joostwijn/Hard_Versus_Soft_Magnetic_Microrobots/4. Microrobots/Designs/Ribbon_Hard_Magnet.SLDPRT

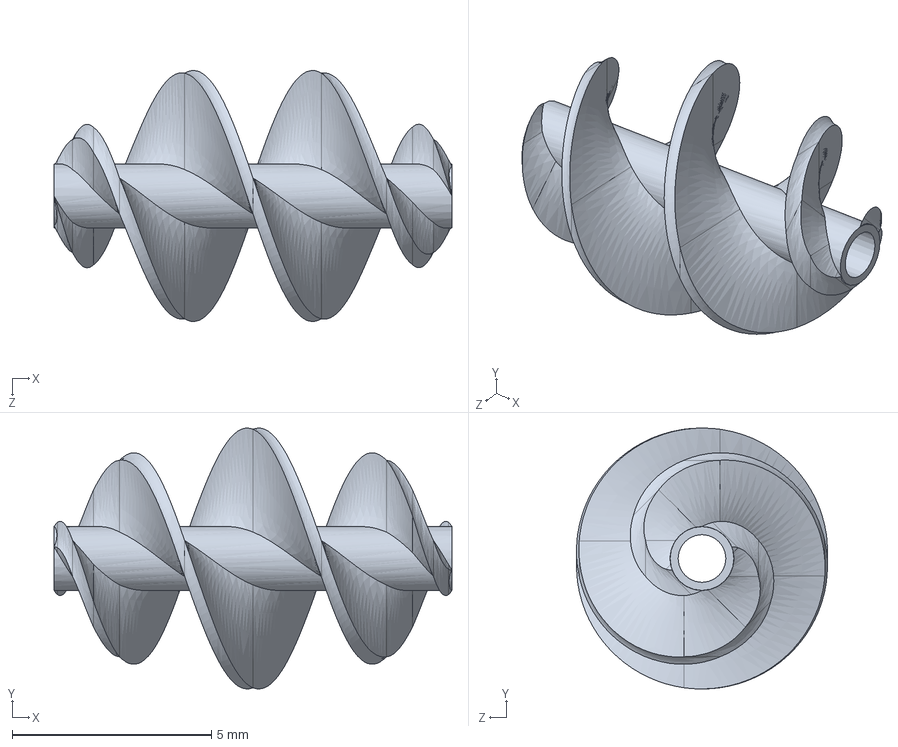
[picture p15: CAD file, 2025-07-08]
4. Microrobots/Designs/Ribbon_Hard_Magnet.SLDPRT
10.00 x 6.55 x 6.31 mm
