joostwijn/Hard_Versus_Soft_Magnetic_Microrobots/1. Rotating Magnetic Field Setup/DXF/PMMA_3mm_1x_FrontP.DXF

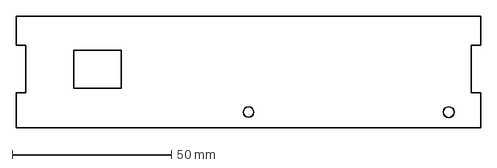
[picture p16: CAD file, 2025-07-07]
1. Rotating Magnetic Field Setup/DXF/PMMA_3mm_1x_FrontP.DXF
146.0 x 35.2 mm
