joostwijn/Hard_Versus_Soft_Magnetic_Microrobots/1. Rotating Magnetic Field Setup/SLDPRT/Plain_Bushing_16x18x20.SLDPRT

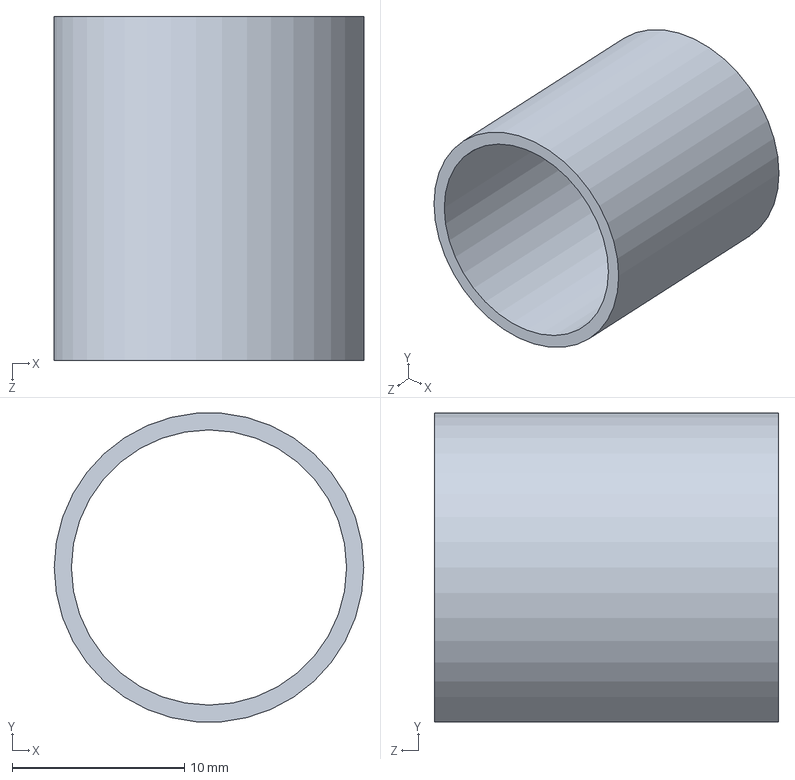
[picture p17: CAD file, 2025-07-07]
1. Rotating Magnetic Field Setup/SLDPRT/Plain_Bushing_16x18x20.SLDPRT
18.0 x 17.9 x 20.0 mm
