joostwijn/Hard_Versus_Soft_Magnetic_Microrobots/4. Microrobots/Designs/Tapered_Helix_Soft_Magnet.SLDPRT

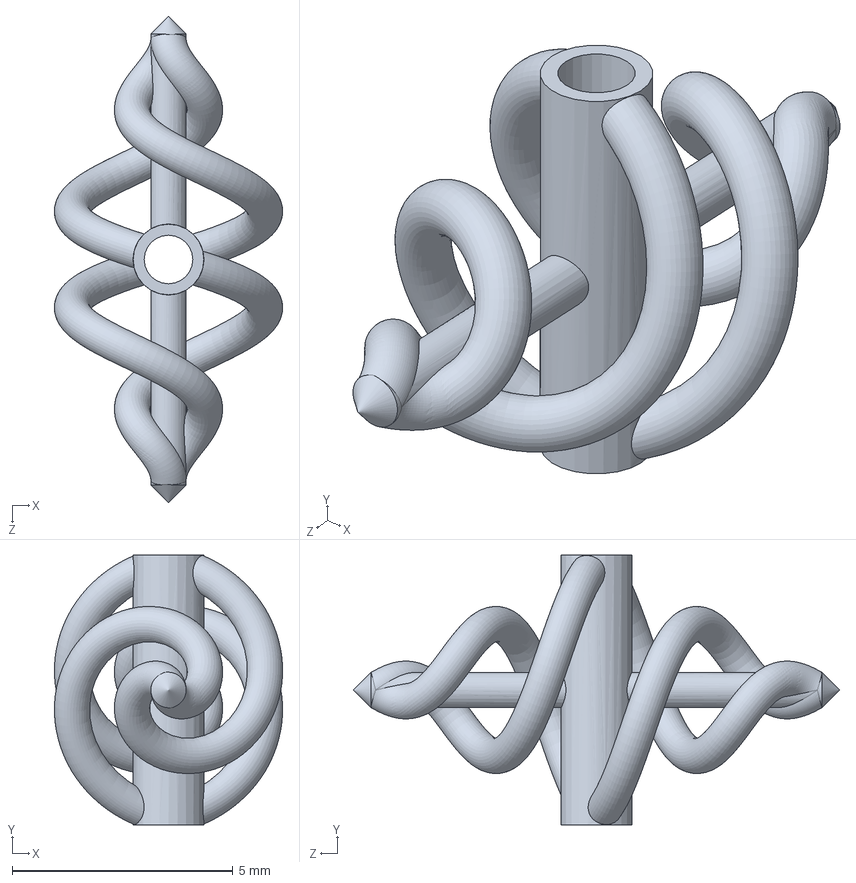
[picture p18: CAD file, 2025-07-08]
4. Microrobots/Designs/Tapered_Helix_Soft_Magnet.SLDPRT
5.16 x 6.10 x 11.0 mm
