joostwijn/Hard_Versus_Soft_Magnetic_Microrobots/1. Rotating Magnetic Field Setup/DXF/PMMA_3mm_1x_RightSP.DXF

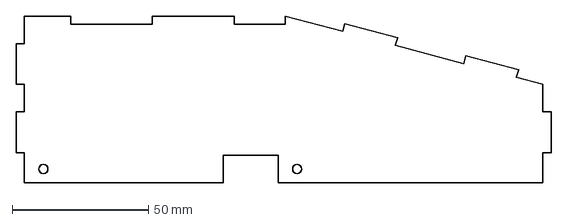
[picture p19: CAD file, 2025-07-07]
1. Rotating Magnetic Field Setup/DXF/PMMA_3mm_1x_RightSP.DXF
196.0 x 61.0 mm
