joostwijn/Hard_Versus_Soft_Magnetic_Microrobots/1. Rotating Magnetic Field Setup/SLDPRT/Slots.SLDPRT

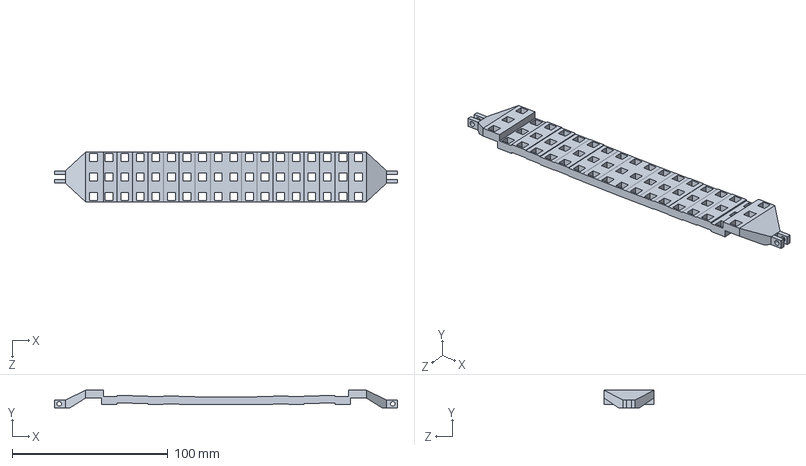
[picture p20: CAD file, 2025-07-07]
1. Rotating Magnetic Field Setup/SLDPRT/Slots.SLDPRT
220.0 x 11.3 x 32.0 mm
