joostwijn/Hard_Versus_Soft_Magnetic_Microrobots/1. Rotating Magnetic Field Setup/SLDPRT/O-Ring_6x1.9.SLDPRT

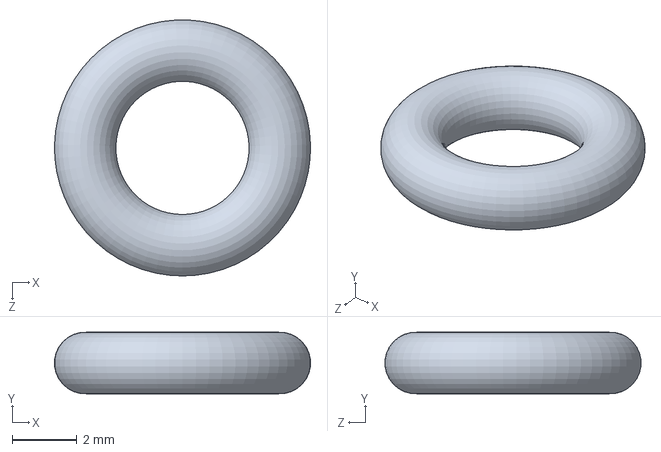
[picture p21: CAD file, 2025-07-07]
1. Rotating Magnetic Field Setup/SLDPRT/O-Ring_6x1.9.SLDPRT
7.89 x 1.90 x 7.88 mm
