joostwijn/Hard_Versus_Soft_Magnetic_Microrobots/1. Rotating Magnetic Field Setup/SLDPRT/Mounting_Bracket_ NEMA17.SLDPRT

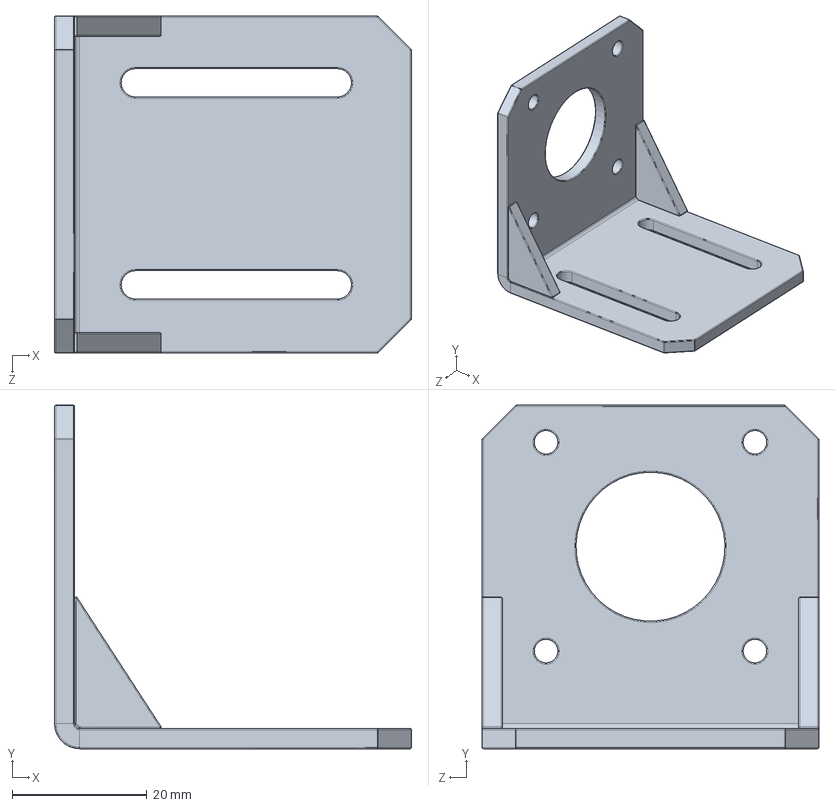
[picture p22: CAD file, 2025-07-07]
1. Rotating Magnetic Field Setup/SLDPRT/Mounting_Bracket_ NEMA17.SLDPRT
53.0 x 51.0 x 50.0 mm
