joostwijn/Hard_Versus_Soft_Magnetic_Microrobots/1. Rotating Magnetic Field Setup/SLDPRT/NX3224T024.SLDPRT

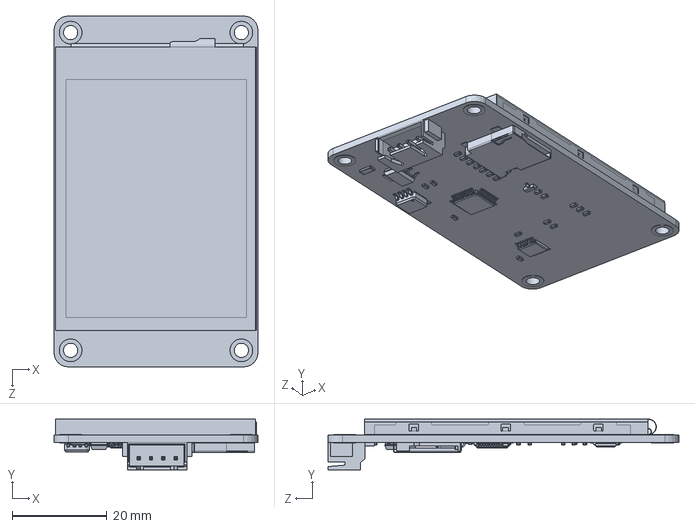
[picture p23: CAD file, 2025-07-07]
1. Rotating Magnetic Field Setup/SLDPRT/NX3224T024.SLDPRT
43.0 x 10.7 x 74.0 mm
