joostwijn/Hard_Versus_Soft_Magnetic_Microrobots/1. Rotating Magnetic Field Setup/SLDPRT/PowerSupply.SLDPRT

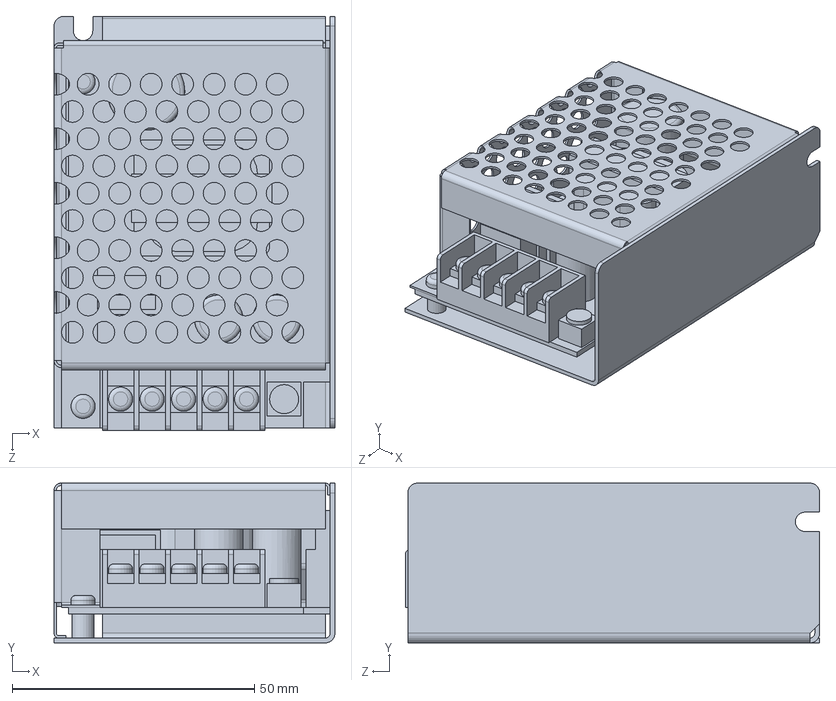
[picture p25: CAD file, 2025-07-07]
1. Rotating Magnetic Field Setup/SLDPRT/PowerSupply.SLDPRT
58.0 x 33.0 x 85.5 mm
