joostwijn/Hard_Versus_Soft_Magnetic_Microrobots/1. Rotating Magnetic Field Setup/SLDPRT/BackPlate.SLDPRT

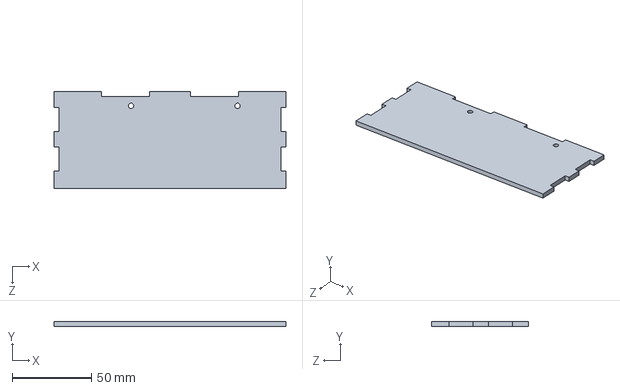
[picture p26: CAD file, 2025-07-07]
1. Rotating Magnetic Field Setup/SLDPRT/BackPlate.SLDPRT
146.0 x 3.00 x 61.0 mm
