joostwijn/Hard_Versus_Soft_Magnetic_Microrobots/1. Rotating Magnetic Field Setup/SLDPRT/Bracket_90deg.SLDPRT

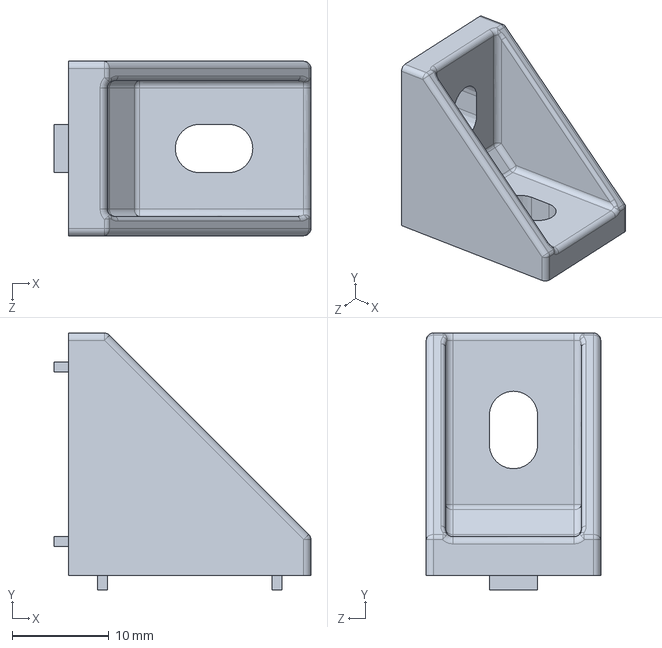
[picture p27: CAD file, 2025-07-07]
1. Rotating Magnetic Field Setup/SLDPRT/Bracket_90deg.SLDPRT
26.5 x 26.5 x 18.0 mm
