joostwijn/Hard_Versus_Soft_Magnetic_Microrobots/1. Rotating Magnetic Field Setup/SLDPRT/Tube_Setter.SLDPRT

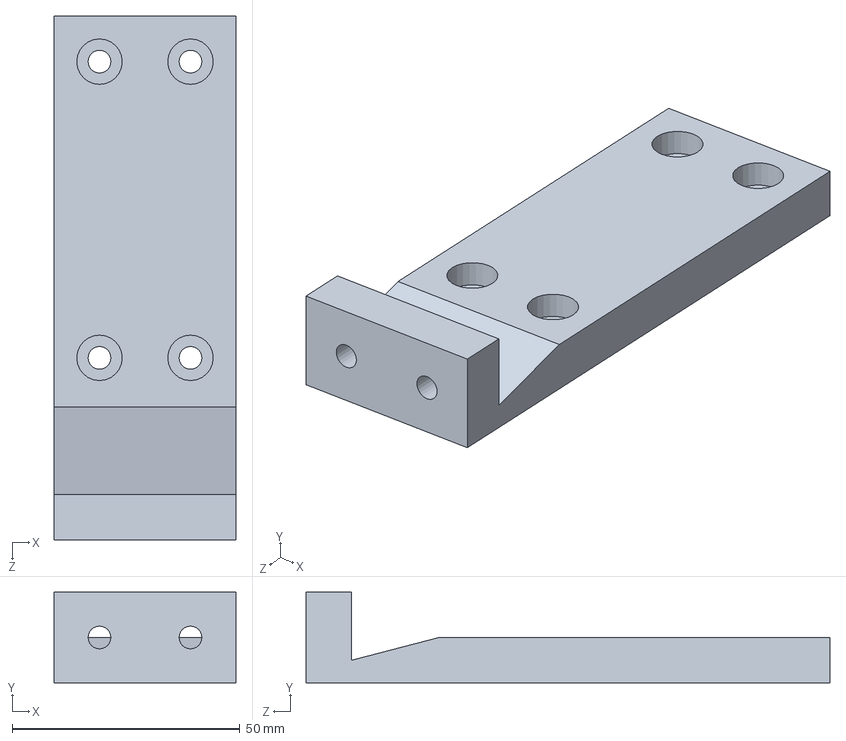
[picture p28: CAD file, 2025-07-07]
1. Rotating Magnetic Field Setup/SLDPRT/Tube_Setter.SLDPRT
40.0 x 20.0 x 115.1 mm
