joostwijn/Hard_Versus_Soft_Magnetic_Microrobots/1. Rotating Magnetic Field Setup/SLDPRT/O-Ring_28x3.1.SLDPRT

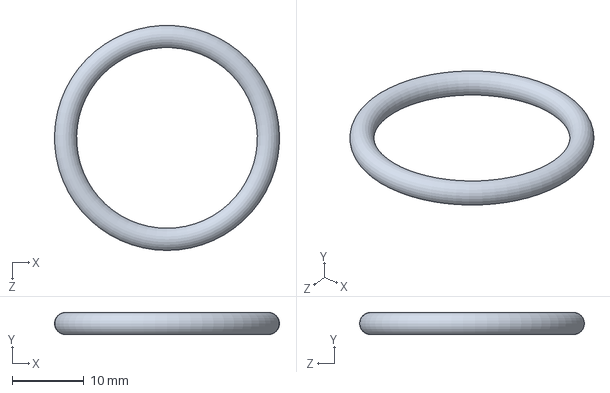
[picture p29: CAD file, 2025-07-07]
1. Rotating Magnetic Field Setup/SLDPRT/O-Ring_28x3.1.SLDPRT
31.4 x 3.10 x 31.4 mm
