joostwijn/Hard_Versus_Soft_Magnetic_Microrobots/1. Rotating Magnetic Field Setup/SLDPRT/FrontPlate.SLDPRT

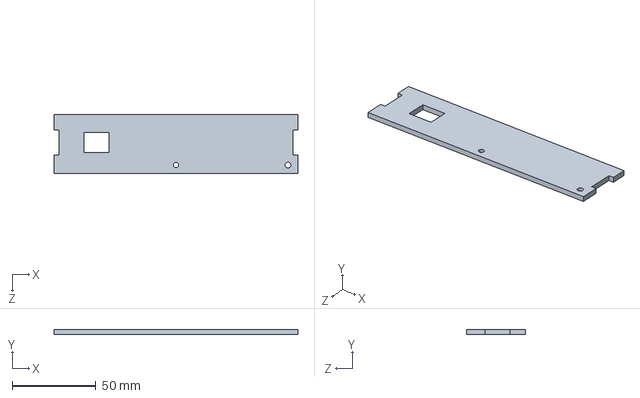
[picture p30: CAD file, 2025-07-07]
1. Rotating Magnetic Field Setup/SLDPRT/FrontPlate.SLDPRT
146.0 x 3.00 x 35.2 mm
