joostwijn/Hard_Versus_Soft_Magnetic_Microrobots/1. Rotating Magnetic Field Setup/SLDPRT/Arduino_UNO_Rev3_Base.SLDPRT

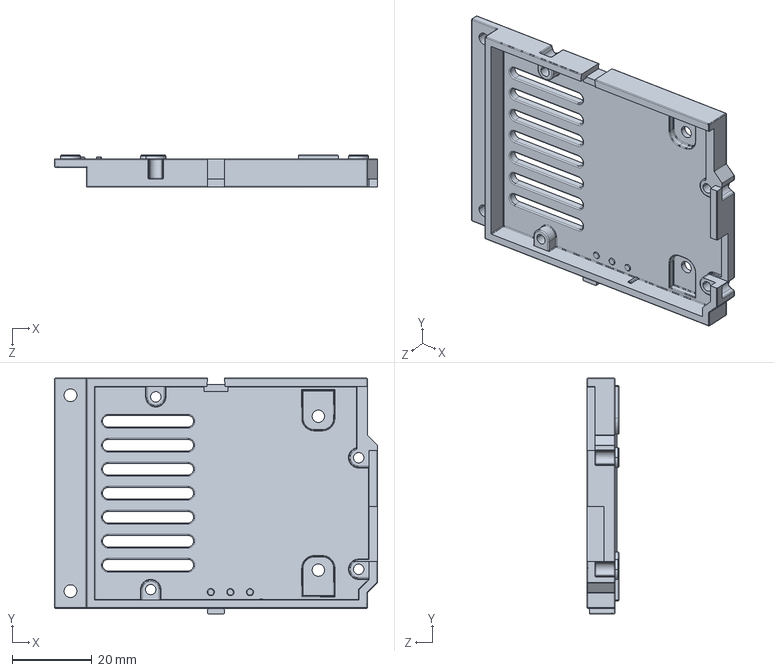
[picture p31: CAD file, 2025-07-07]
1. Rotating Magnetic Field Setup/SLDPRT/Arduino_UNO_Rev3_Base.SLDPRT
80.8 x 59.0 x 8.00 mm
