joostwijn/Hard_Versus_Soft_Magnetic_Microrobots/1. Rotating Magnetic Field Setup/SLDPRT/Tube_Cap.SLDPRT

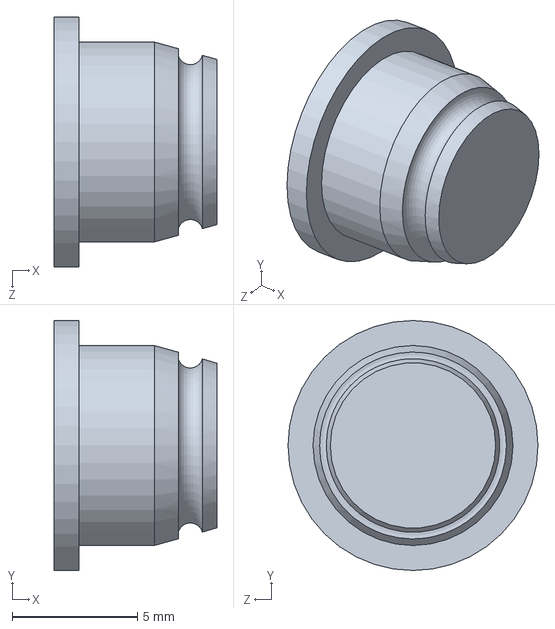
[picture p32: CAD file, 2025-07-07]
1. Rotating Magnetic Field Setup/SLDPRT/Tube_Cap.SLDPRT
6.50 x 10.0 x 10.0 mm
