joostwijn/Hard_Versus_Soft_Magnetic_Microrobots/1. Rotating Magnetic Field Setup/SLDPRT/Tube_12x8x220.SLDPRT

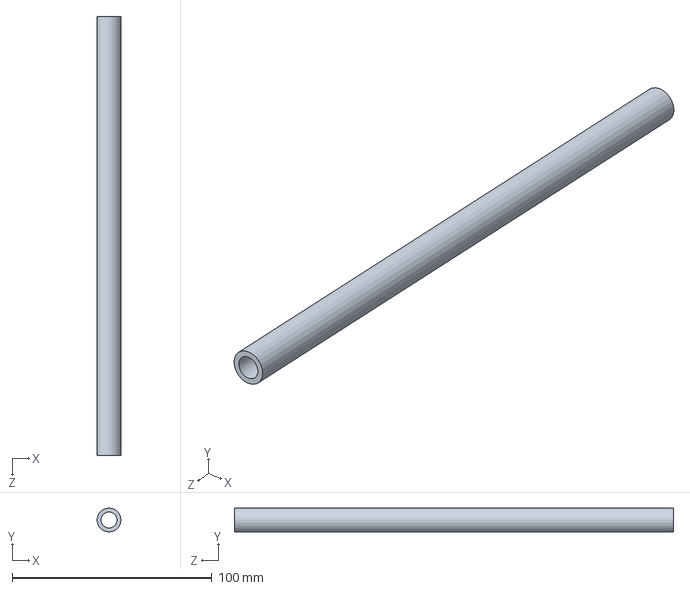
[picture p33: CAD file, 2025-07-07]
1. Rotating Magnetic Field Setup/SLDPRT/Tube_12x8x220.SLDPRT
12.0 x 12.0 x 220.0 mm
