joostwijn/Hard_Versus_Soft_Magnetic_Microrobots/1. Rotating Magnetic Field Setup/SLDPRT/TopPlate_Back.SLDPRT

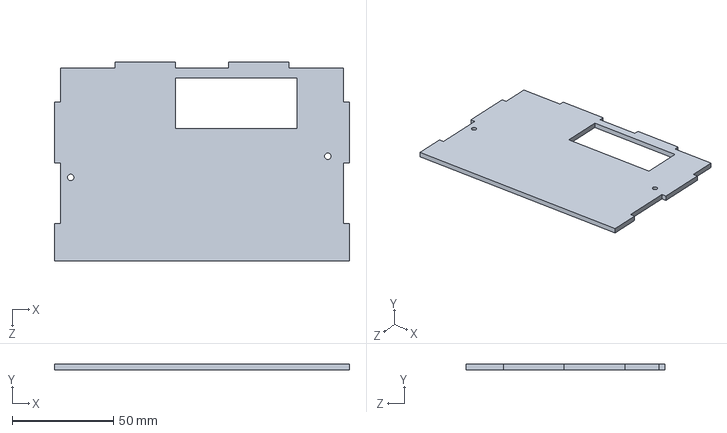
[picture p34: CAD file, 2025-07-07]
1. Rotating Magnetic Field Setup/SLDPRT/TopPlate_Back.SLDPRT
146.0 x 3.00 x 98.7 mm
