joostwijn/Hard_Versus_Soft_Magnetic_Microrobots/1. Rotating Magnetic Field Setup/SLDPRT/2020_Single_ALPROFILE_500mm.SLDPRT

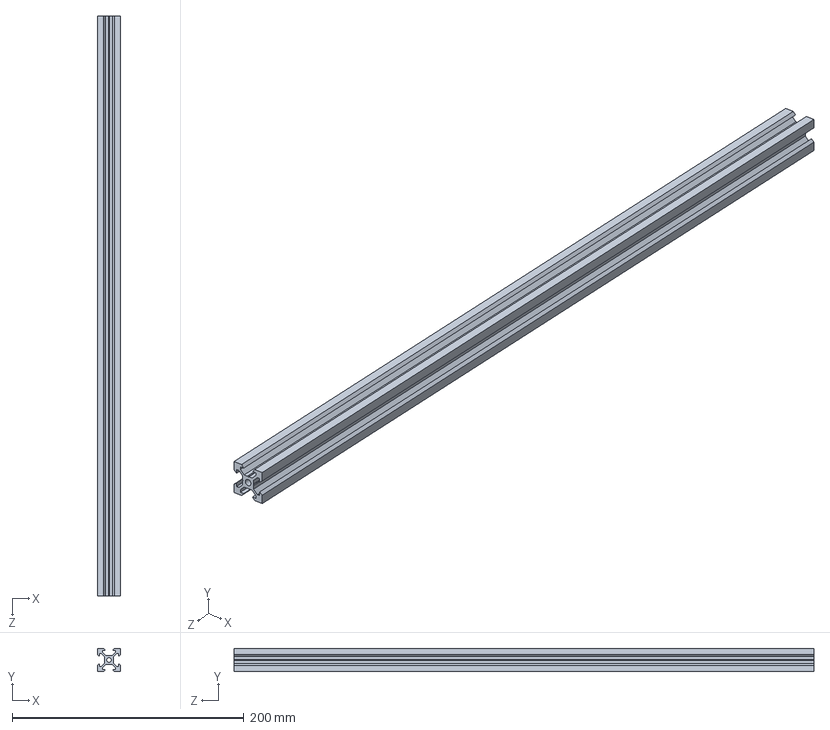
[picture p35: CAD file, 2025-07-07]
1. Rotating Magnetic Field Setup/SLDPRT/2020_Single_ALPROFILE_500mm.SLDPRT
20.0 x 20.0 x 500.0 mm
