joostwijn/Hard_Versus_Soft_Magnetic_Microrobots/1. Rotating Magnetic Field Setup/SLDPRT/Axis.SLDPRT

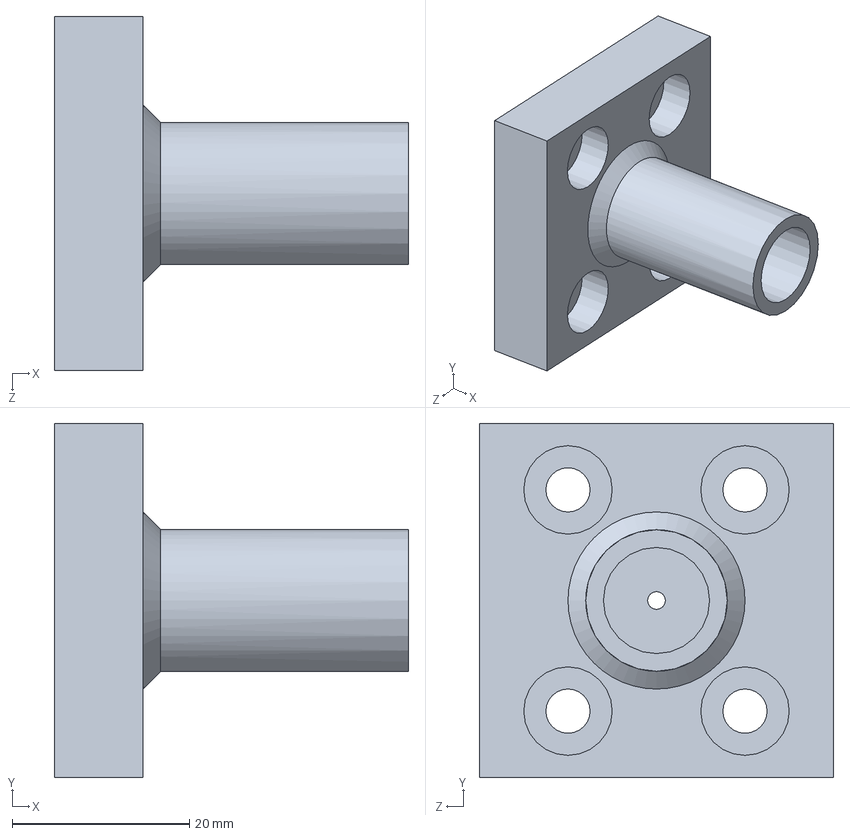
[picture p36: CAD file, 2025-07-07]
1. Rotating Magnetic Field Setup/SLDPRT/Axis.SLDPRT
40.0 x 40.0 x 40.0 mm
