joostwijn/Hard_Versus_Soft_Magnetic_Microrobots/1. Rotating Magnetic Field Setup/SLDPRT/Connector_Switch_And_Fuse.SLDPRT

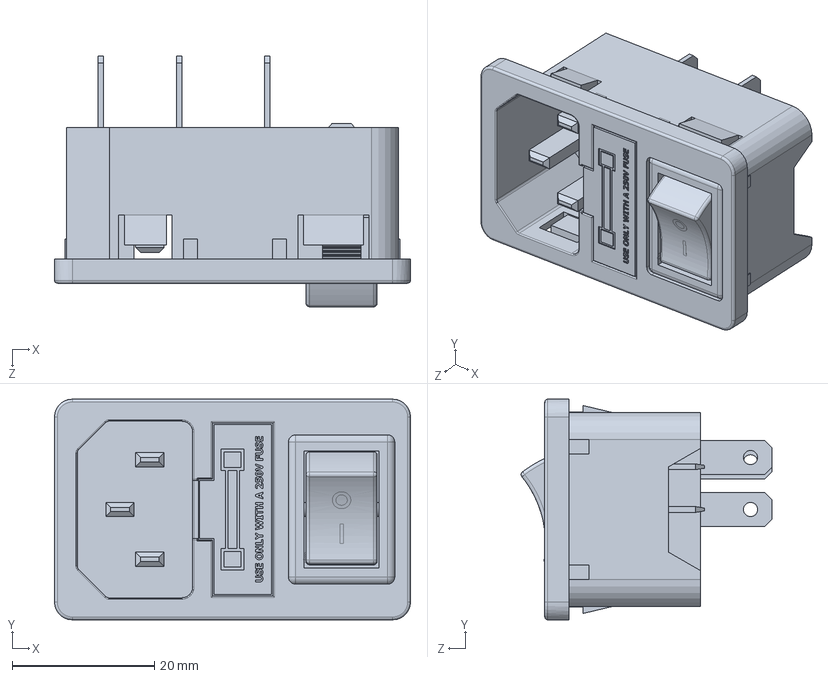
[picture p37: CAD file, 2025-07-07]
1. Rotating Magnetic Field Setup/SLDPRT/Connector_Switch_And_Fuse.SLDPRT
50.0 x 31.0 x 35.2 mm
