joostwijn/Hard_Versus_Soft_Magnetic_Microrobots/1. Rotating Magnetic Field Setup/SLDPRT/2040_Double_ALPROFILE_160mm.SLDPRT

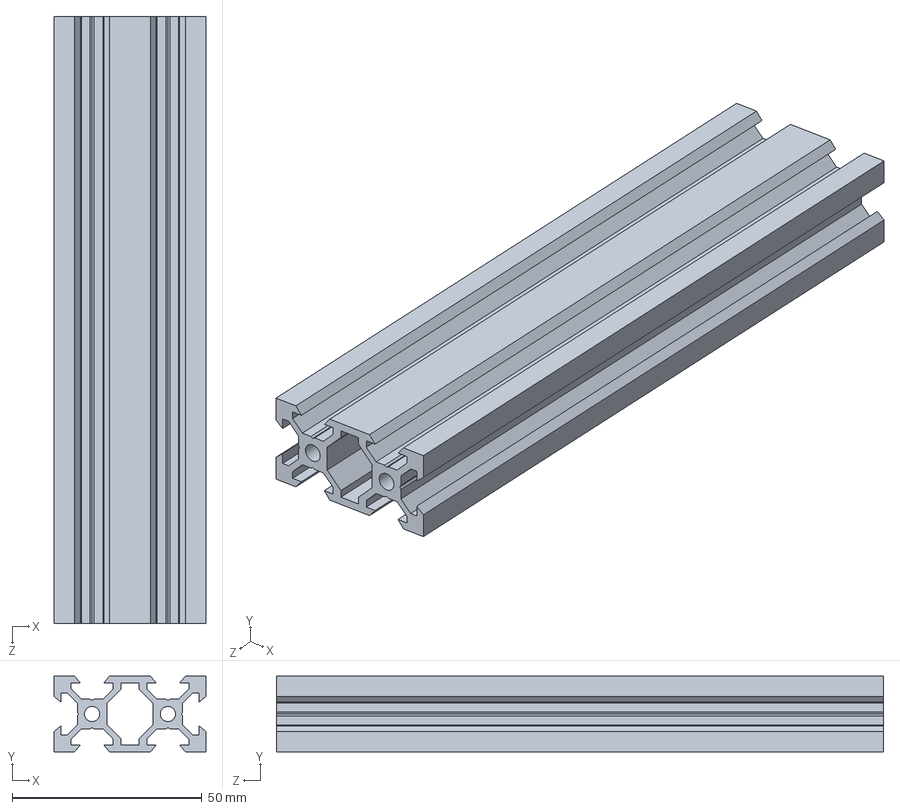
[picture p38: CAD file, 2025-07-07]
1. Rotating Magnetic Field Setup/SLDPRT/2040_Double_ALPROFILE_160mm.SLDPRT
40.0 x 20.0 x 160.0 mm
