joostwijn/Hard_Versus_Soft_Magnetic_Microrobots/1. Rotating Magnetic Field Setup/SLDPRT/Right_Sideplate.SLDPRT

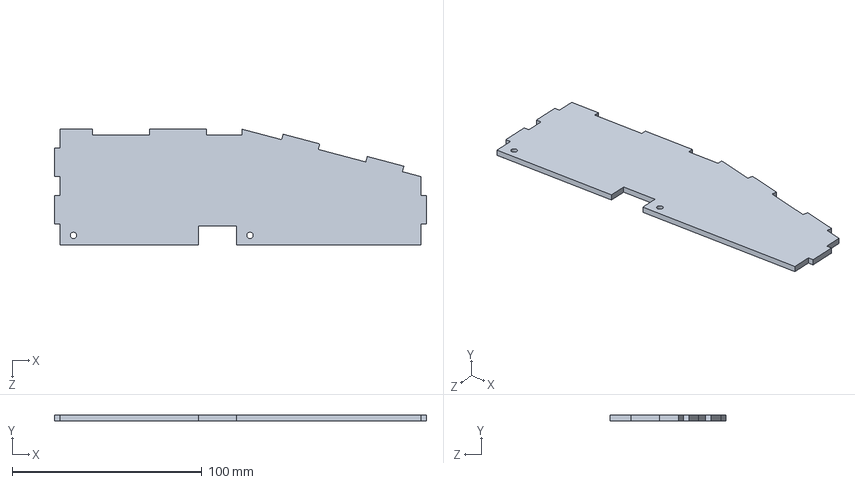
[picture p39: CAD file, 2025-07-07]
1. Rotating Magnetic Field Setup/SLDPRT/Right_Sideplate.SLDPRT
196.0 x 3.00 x 61.0 mm
